s-light/LEDBoard_4x4_16bit/export/3d/LEDBoard_4x4_16bit_rendering.png

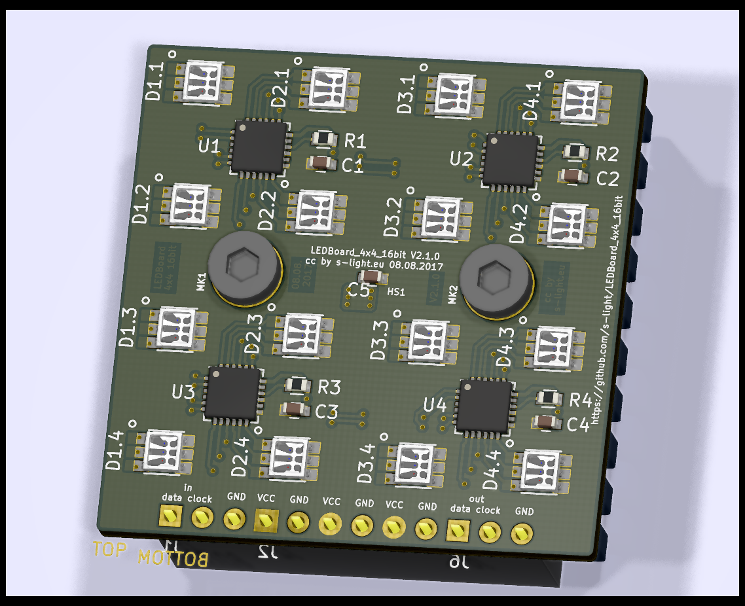
export/3d/LEDBoard_4x4_16bit_rendering.png
